chihauccisoilconte/agnosticbox/agonstic box 3D models/STL/3.2 - jack element 2 (bearing).stl

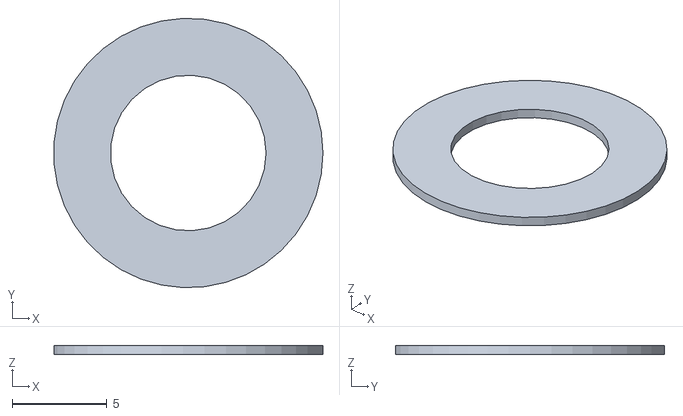
[picture p15: CAD file, 2026-05-21]
agonstic box 3D models/STL/3.2 - jack element 2 (bearing).stl
14.2 x 14.2 x 0.5
