chihauccisoilconte/agnosticbox/agonstic box 3D models/STL/6 - knob element.stl

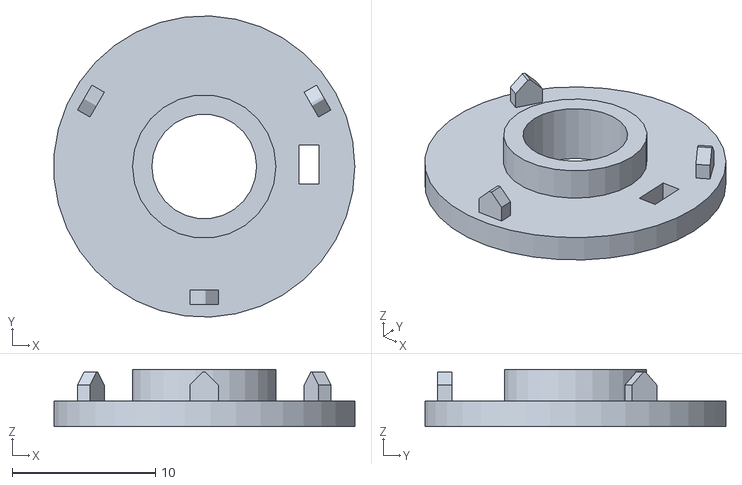
[picture p16: CAD file, 2026-05-21]
agonstic box 3D models/STL/6 - knob element.stl
21.0 x 21.0 x 4.00
