chihauccisoilconte/agnosticbox/agonstic box 3D models/agnostic_box_nano_3d_models/leg_element.FCStd

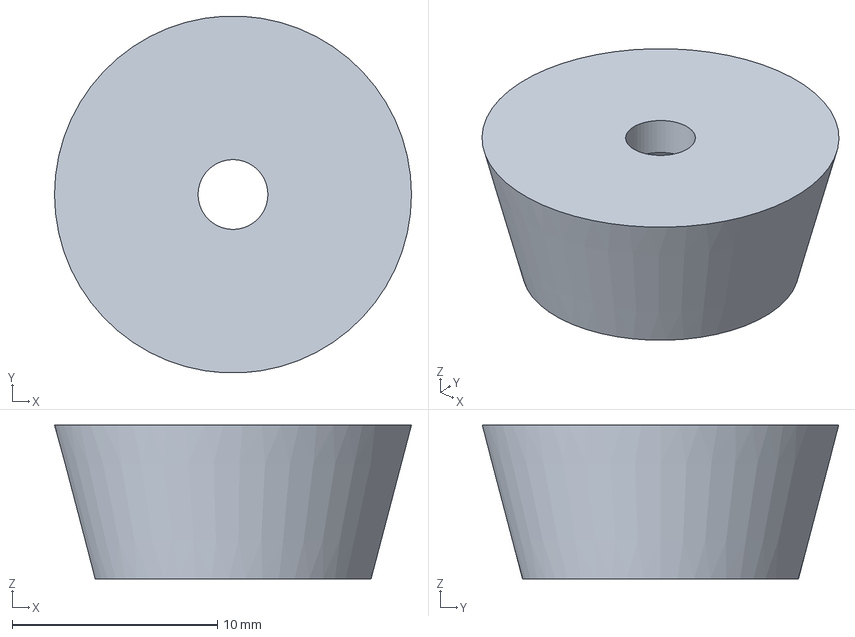
[picture p17: CAD file, 2026-05-21]
agonstic box 3D models/agnostic_box_nano_3d_models/leg_element.FCStd
17.4 x 17.4 x 7.50 mm
