chihauccisoilconte/agnosticbox/agonstic box 3D models/STL/leg - element.stl

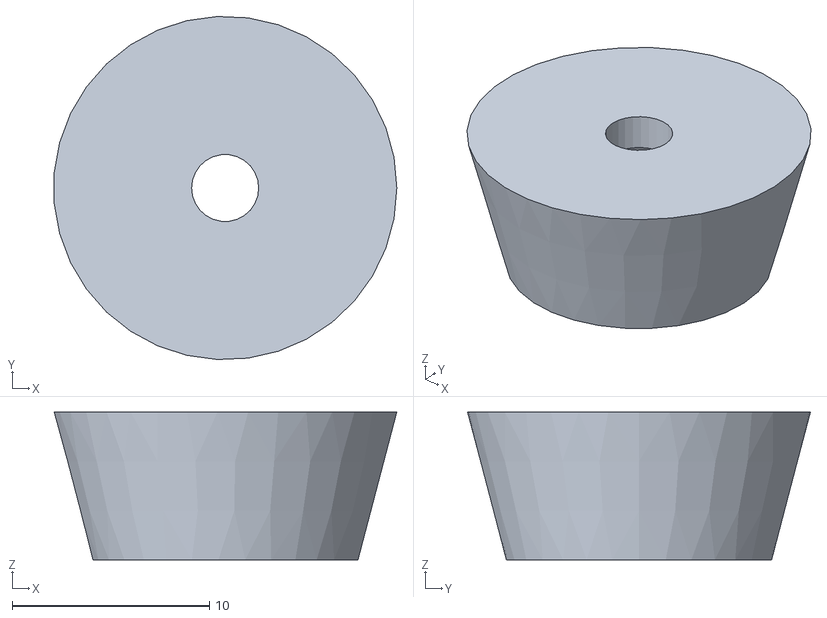
[picture p18: CAD file, 2026-05-21]
agonstic box 3D models/STL/leg - element.stl
17.4 x 17.4 x 7.50
