chihauccisoilconte/agnosticbox/agonstic box 3D models/STL/1 - base.stl

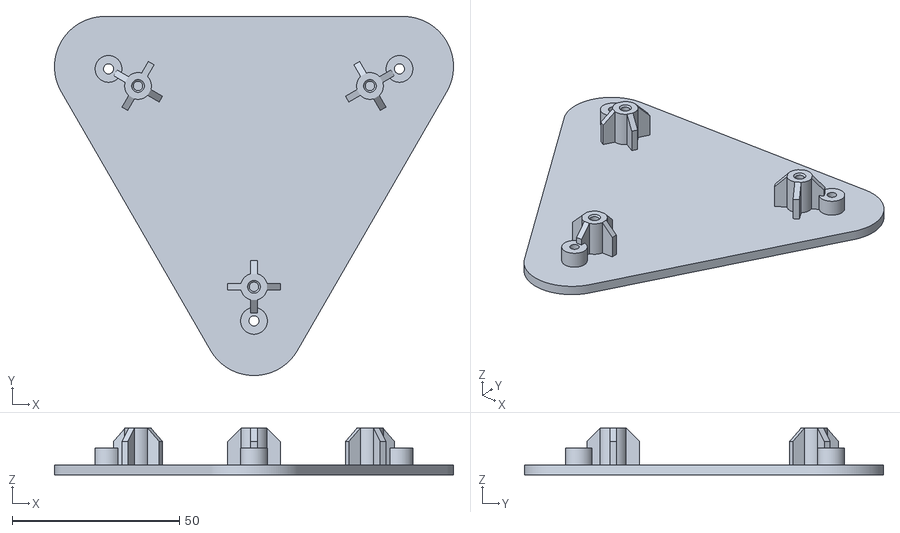
[picture p19: CAD file, 2026-05-21]
agonstic box 3D models/STL/1 - base.stl
119.2 x 107.2 x 14.0
